Blaze-Pascal/EKA-PiF-MCU_PSU/plots/RigolDS4.png

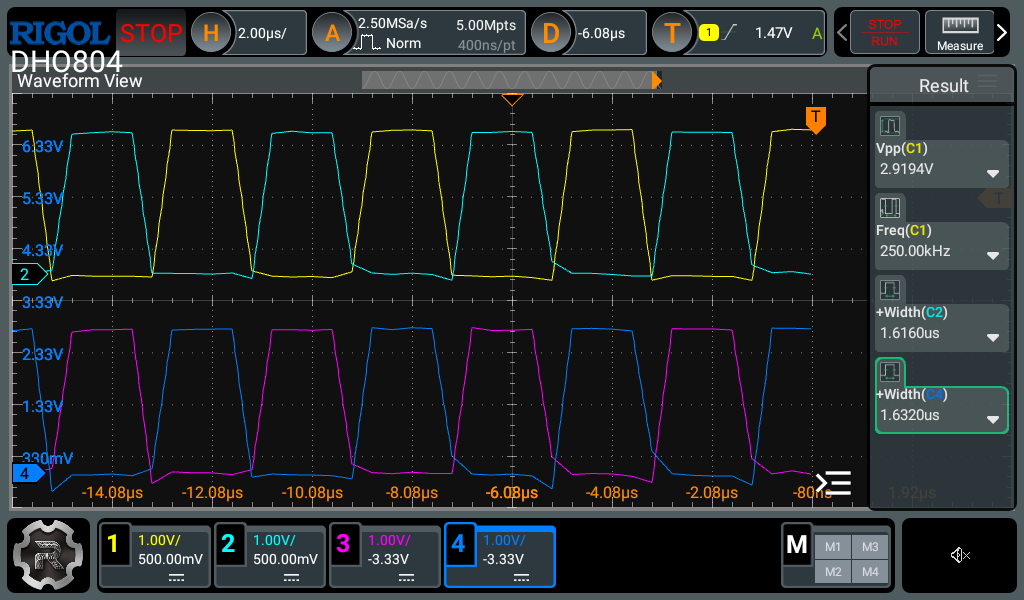
plots/RigolDS4.png
