Blaze-Pascal/EKA-PiF-MCU_PSU/plots/RigolDS7.png

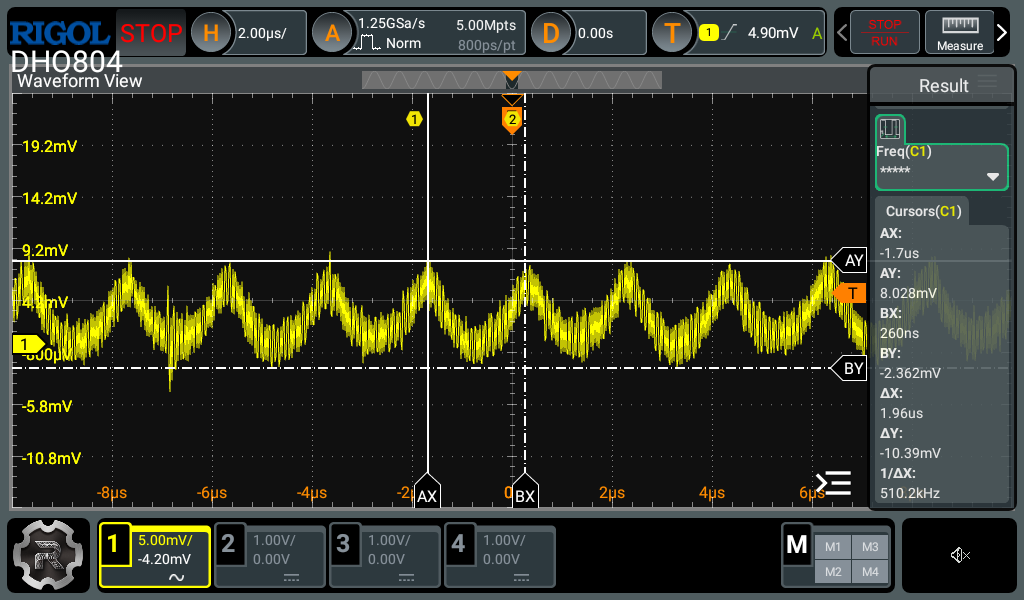
plots/RigolDS7.png
