Blaze-Pascal/EKA-PiF-MCU_PSU/plots/RigolDS11.png

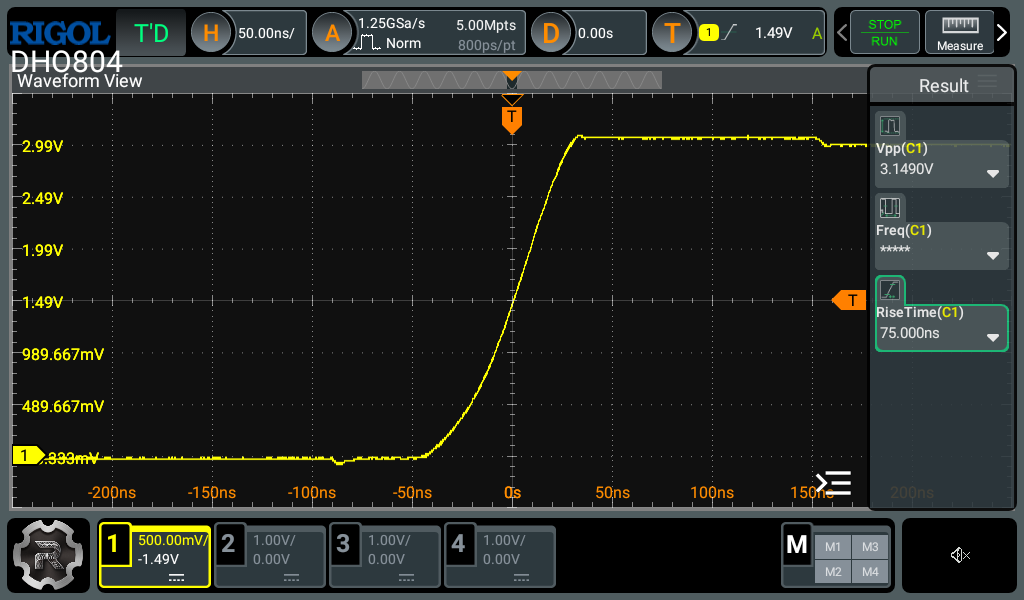
plots/RigolDS11.png
