Blaze-Pascal/EKA-PiF-MCU_PSU/plots/RigolDS12.png

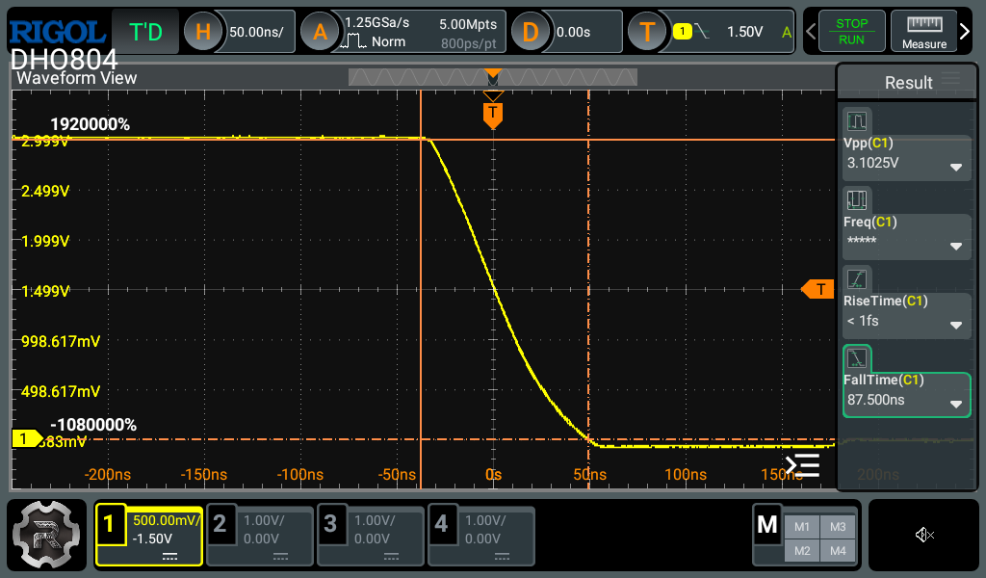
plots/RigolDS12.png
